eltoozero/lol-gbz_3dparts/img/gbz_inside_open.jpg

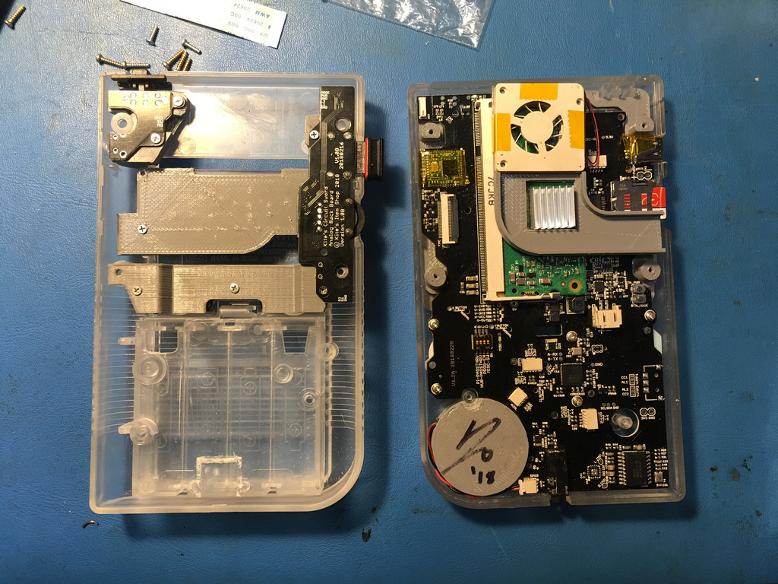
img/gbz_inside_open.jpg
