eltoozero/lol-gbz_3dparts/img/gbz_outside_open.jpg

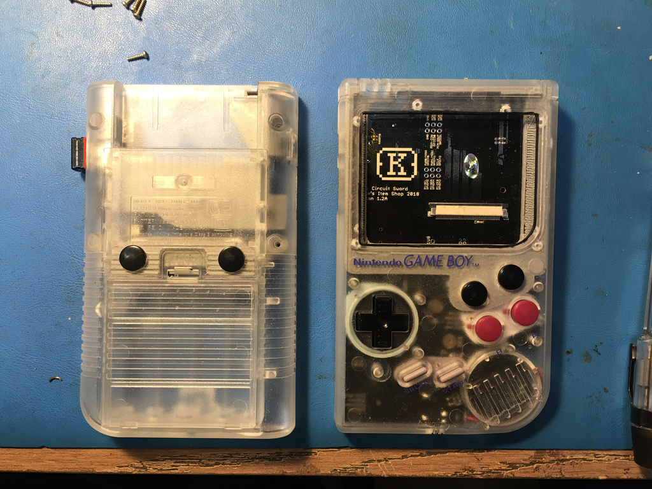
img/gbz_outside_open.jpg
